NilsFC/Model-H-Rmx/Pics/IMG_2830.jpg

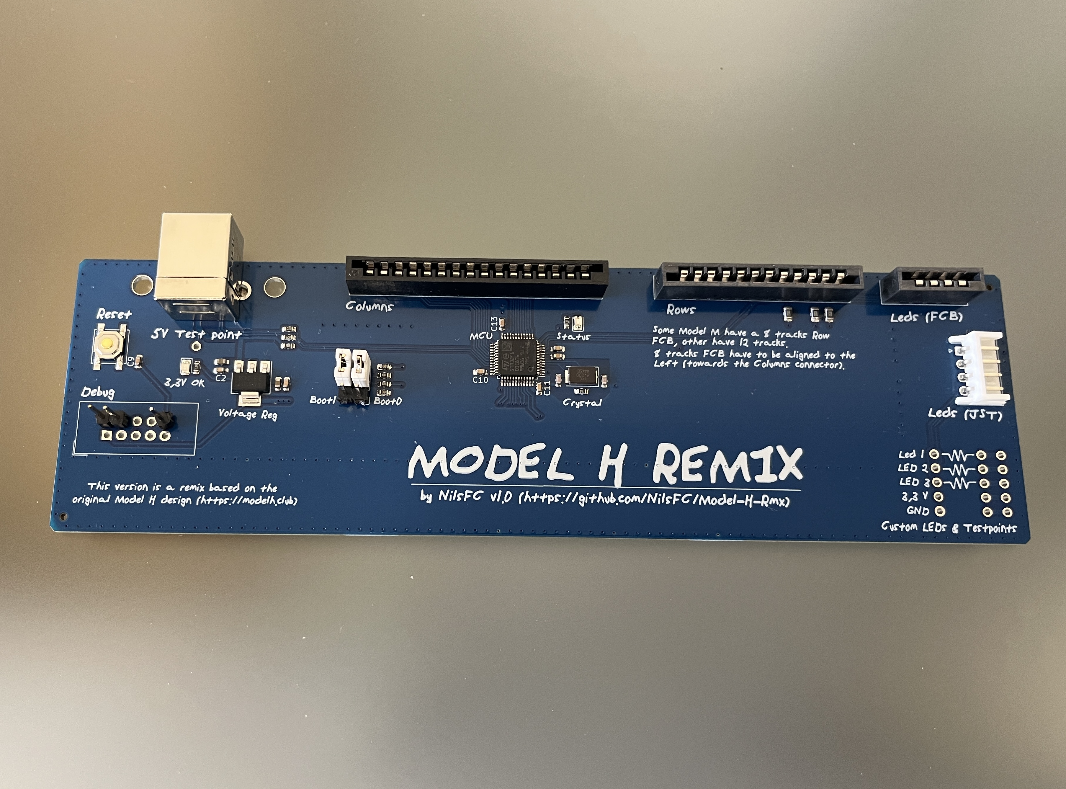
Pics/IMG_2830.jpg
