NilsFC/Model-H-Rmx/Pics/IMG_2831.jpg

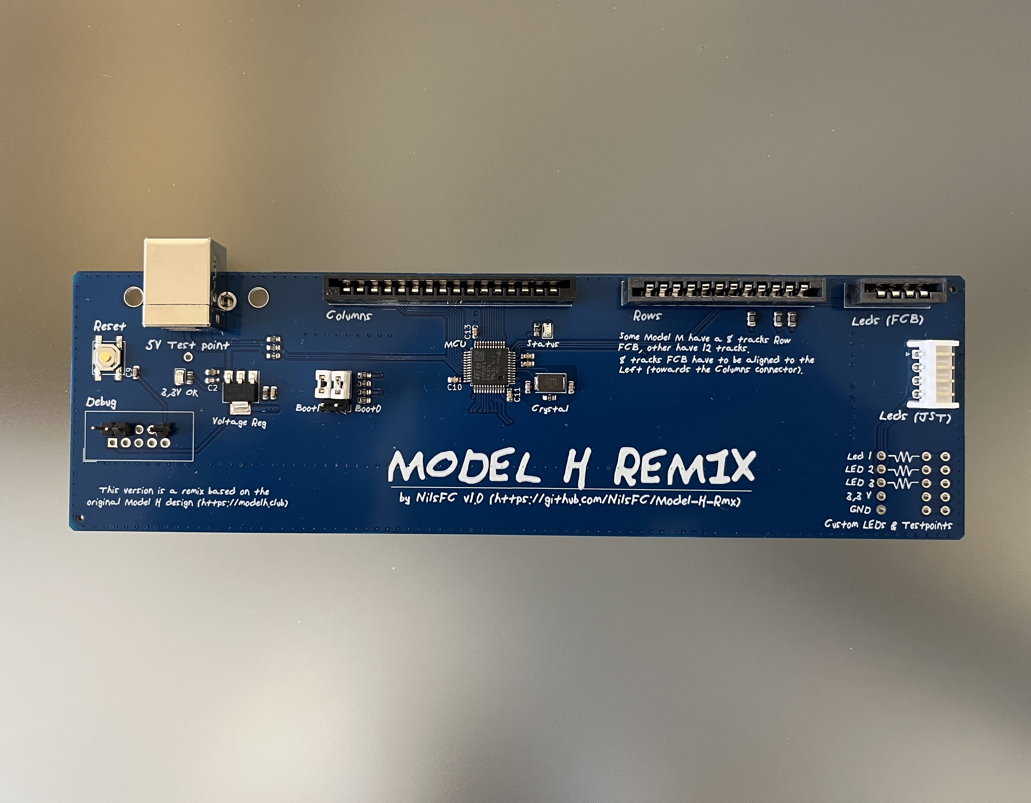
Pics/IMG_2831.jpg
