NilsFC/Model-H-Rmx/Pics/IMG_2832.jpg

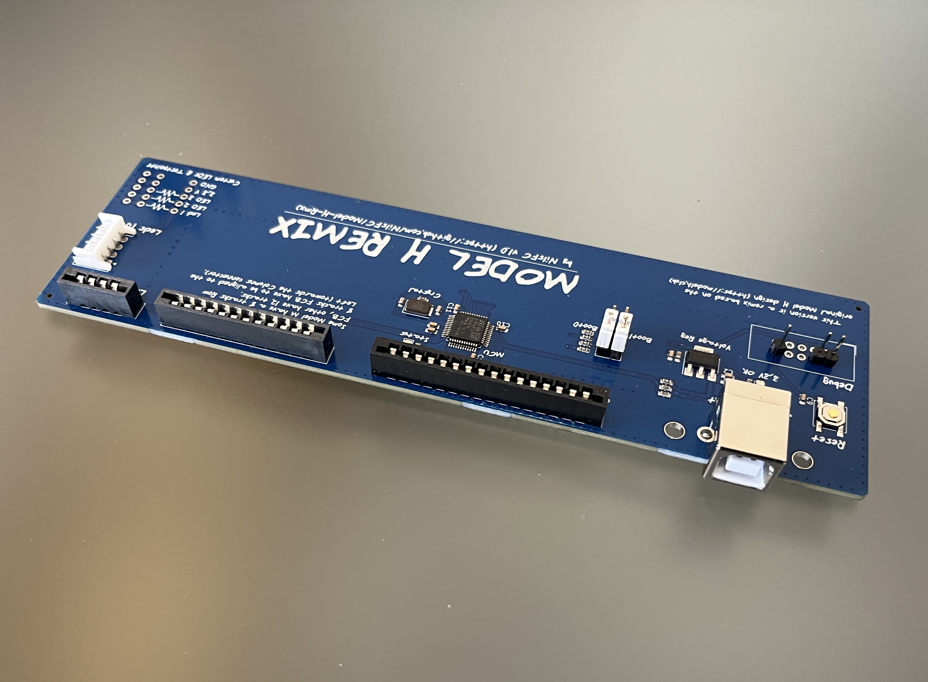
Pics/IMG_2832.jpg
