NilsFC/Model-H-Rmx/Pics/IMG_2833.jpg

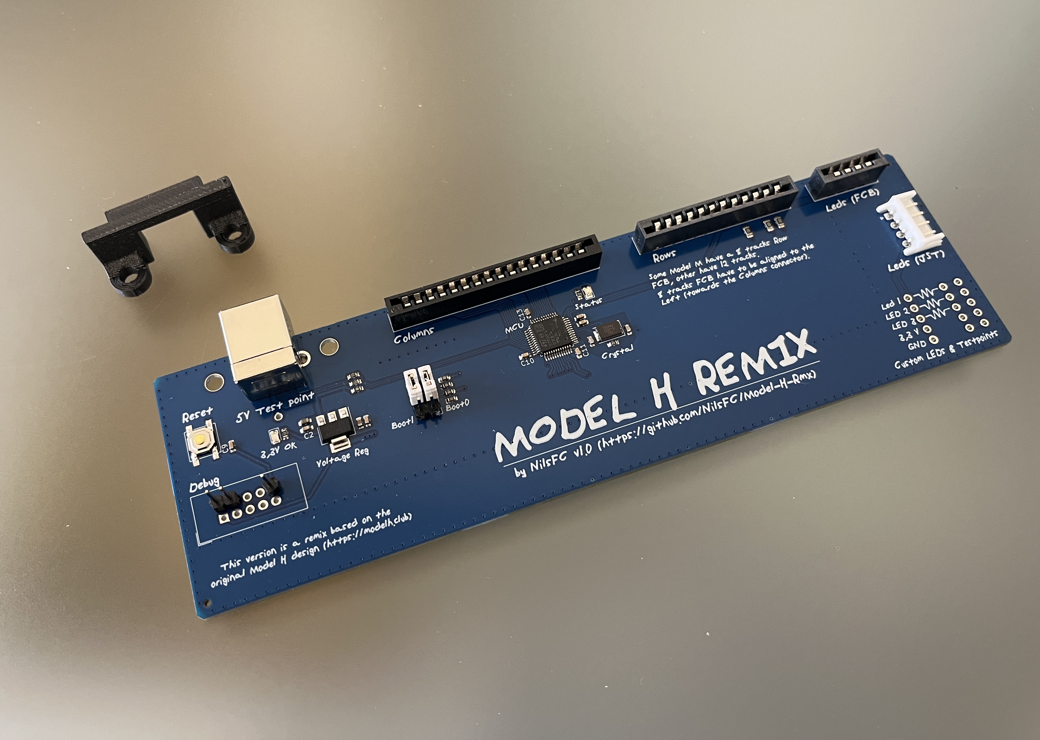
Pics/IMG_2833.jpg
