NilsFC/Model-H-Rmx/Pics/IMG_2834.jpg

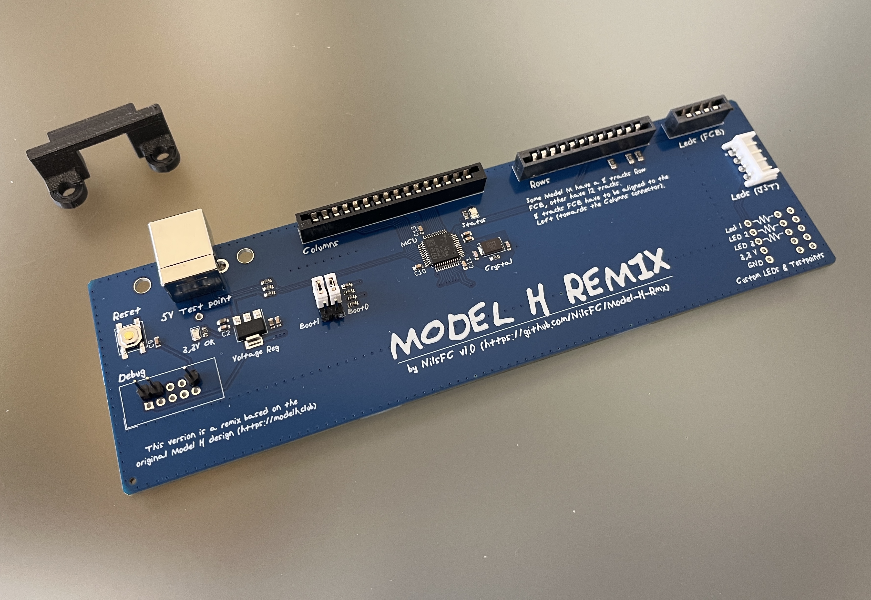
Pics/IMG_2834.jpg
