NilsFC/Model-H-Rmx/Pics/IMG_2835.jpg

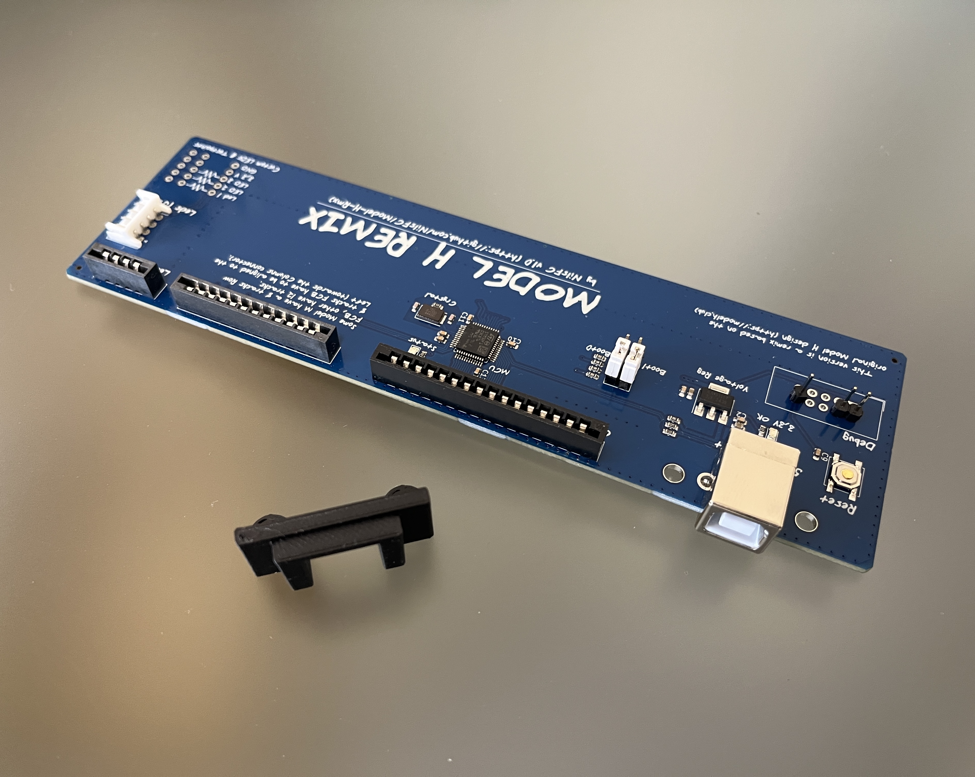
Pics/IMG_2835.jpg
