NilsFC/Model-H-Rmx/Pics/IMG_2836.jpg

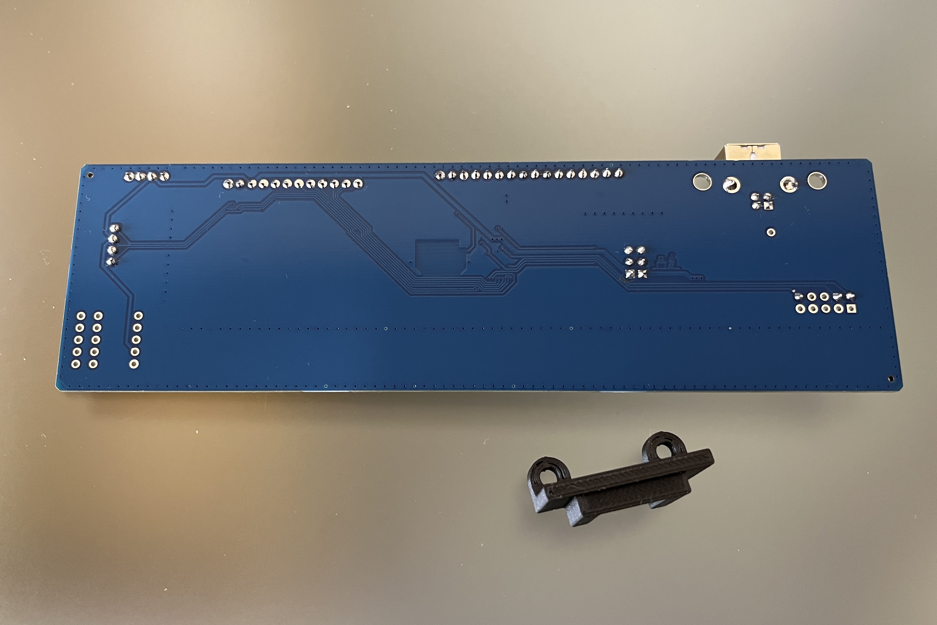
Pics/IMG_2836.jpg
