NilsFC/Model-H-Rmx/site/pics/ST-Link connection.png

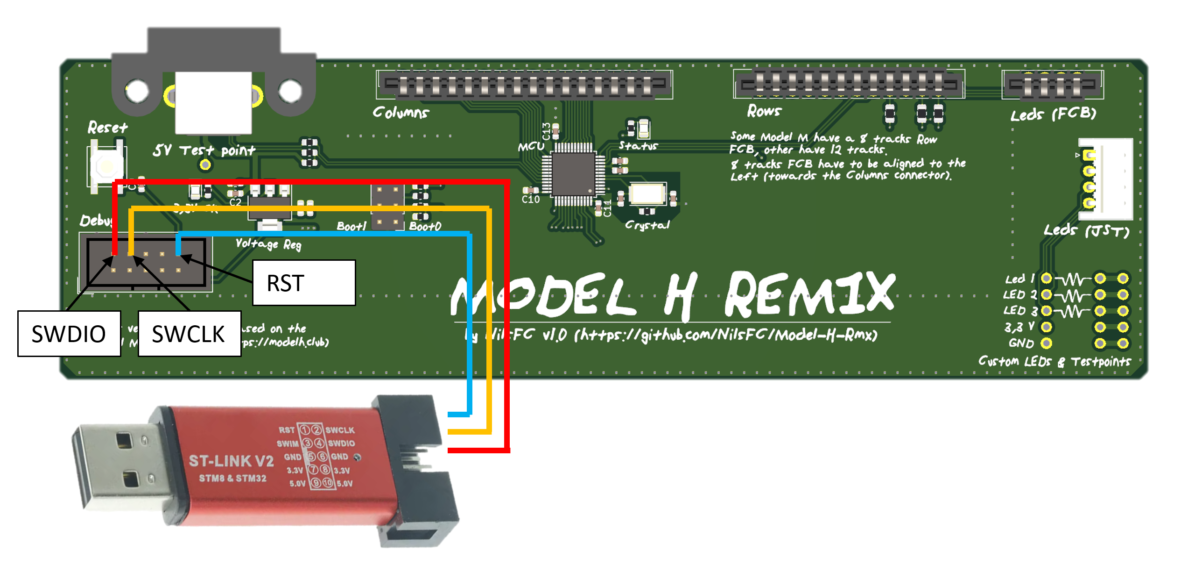
site/pics/ST-Link connection.png
